bkifft/MK-312WS/kicad/mk312ws.kicad_sch

## KiCad design kicad/mk312ws.kicad_sch (2022-05-07)

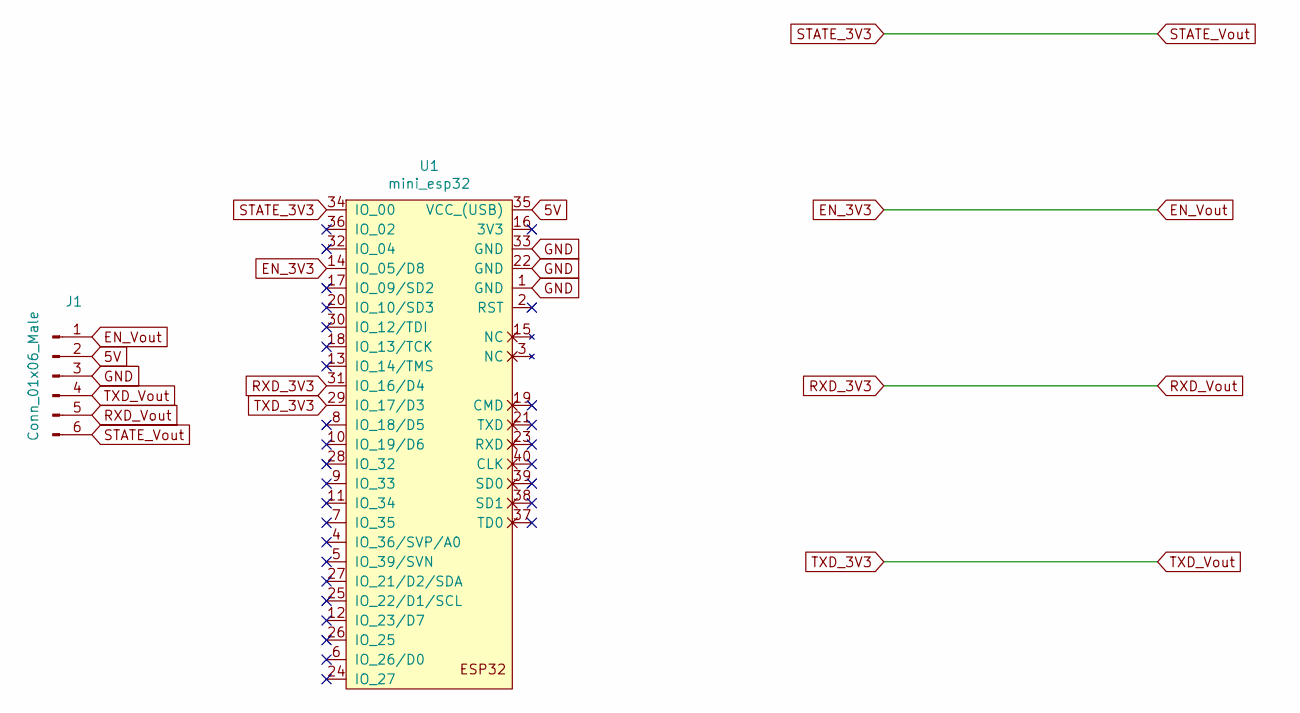
[picture p5: schematic mk312ws.kicad_sch]

Parts:
J1: Conn_01x06_Male; PinHeader_1x06_P2.54mm_Horizontal
U1: mini_esp32; ESP32_mini

Connections:
5V: J1.2, U1.35 (VCC_(USB))
EN_3V3: J1.1, U1.14 (IO_05/D8)
GND: J1.3, U1.1 (GND), U1.22 (GND), U1.33 (GND)
RXD_3V3: J1.5, U1.31 (IO_16/D4)
STATE_3V3: J1.6, U1.34 (IO_00)
TXD_3V3: J1.4, U1.29 (IO_17/D3)
